floppydisk525/RnanoBot/board/datasheets/lsm9ds1 external cap note image.PNG

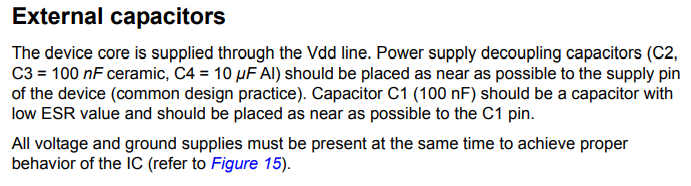
board/datasheets/lsm9ds1 external cap note image.PNG
